eccentricOrange/bt-speaker/simulations/full/ab-power-amp.asc

Q1: pnp; Qtip32a
Q2: npn; Qtip31a
Q3: npn; Qtip31a
Q4: pnp; Qtip32a
R1: res; 400R
R2: res; 400R
R3: res; 1R
R4: res; 1R
RA1: res; 1k
RA2: res; 1k
Named nets: +Vcc, -Vcc, Vo, Vi
.lib libraries/tip31a.lib
.lib libraries/tip32a.lib
