eccentricOrange/bt-speaker/simulations/full/main.asc

C1: cap; 1mF
C2: cap; 1mF
C_HPF: cap; 10µF
C_LPF: cap; 10µF
R1: res; 10k
R2: res; 10k
R_HPF: res; 12R
R_LPF: res; 12R
Rf1: res; 6.2k
Rf2: res; 6.2k
Ri1: res; 1k
Ri2: res; 1k
RL1: res; 4R
RL2: res; 4R
U1: UniversalOpAmp
U2: UniversalOpAmp
V+: voltage; 24V
Vs: voltage; SINE(0 AC 1)
X1: ab-power-amp
X2: ab-power-amp
Named nets: +Vcc, 0, -Vcc, Vs, V_LPF, V_HPF, Vo1, Vo2
.ac dec 100 1Hz 20e3Hz
CLASS AB AMP
CLASS AB AMP
.tran 0 5ms 0 5us
