eccentricOrange/bt-speaker/simulations/amplifier/a-amp/a-amp.asc

C1: cap; 1µF
Q1: npn
R1: res; 14k
R2: res; 10k
RC: res; 80
RE: res; 80
RL: res; 100
V+: voltage; 2.5V
V-: voltage; -2.5V
Vs: voltage; SINE(0 100m 20k)
Named nets: 0, +Vcc, -Vcc, Vi, Vo
.tran 0 500us 0 5us
