eccentricOrange/bt-speaker/simulations/amplifier/ab-power-amp/ab-power-amp.asc

Q1: pnp; Qtip32a
Q2: npn; Qtip31a
Q3: npn; Qtip31a
Q4: pnp; Qtip32a
R1: res; 400R
R2: res; 400R
R3: res; 1R
R4: res; 1R
RA1: res; 1k
RA2: res; 1k
RL: res; 4R
V1: voltage; 12V
V2: voltage; -12V
Vs: voltage; SINE(0 AC 6)
Named nets: +Vcc, -Vcc, 0, Vi, Vo
.lib libraries/tip31a.lib
.lib libraries/tip32a.lib
.ac dec 100 1Hz 1e+6Hz
.tran 0 500us 0 500ns
