eccentricOrange/bt-speaker/simulations/amplifier/ab-signal-amp/ab-signal-amp.asc

C1: cap; 1µ
C2: cap; 1m
D1: diode
D2: diode
Q1: npn
Q2: pnp
Q3: npn
R1: res; 1k
R2: res; 100
R4: res; 100k
R5: res; 15k
RL: res; 4
V1: voltage; 15
V2: voltage; SINE(0 500m 1kHz)
Named nets: 0, Vcc, Vs, Vo
.ac dec 20 1 20k
.tran 0 2ms 0 20ns
